RiqueFR/CarrinhoAcel/Esq_Eagle/Carrinho/CarrinhoEsq.png

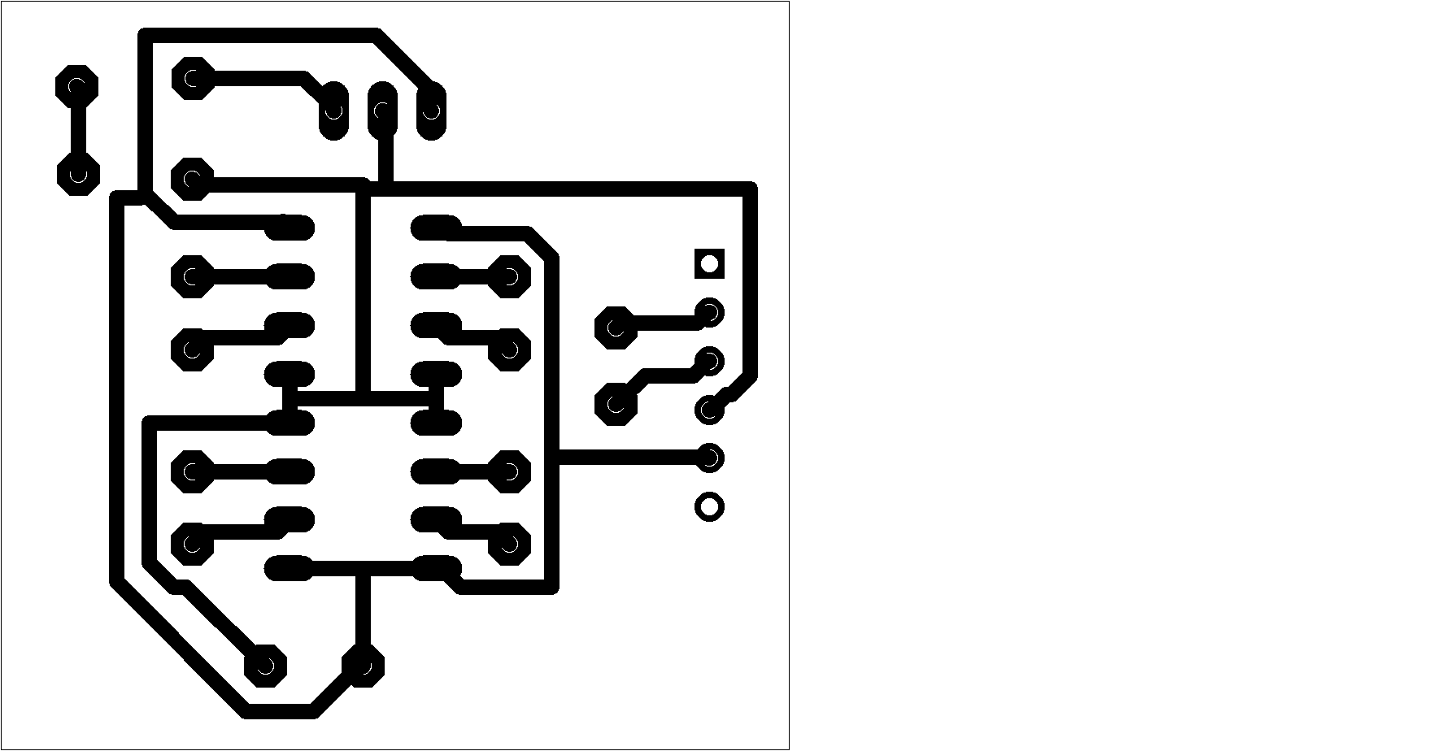
Esq_Eagle/Carrinho/CarrinhoEsq.png
